sanoojes/SplitKeeb/images/day3/handmade.png

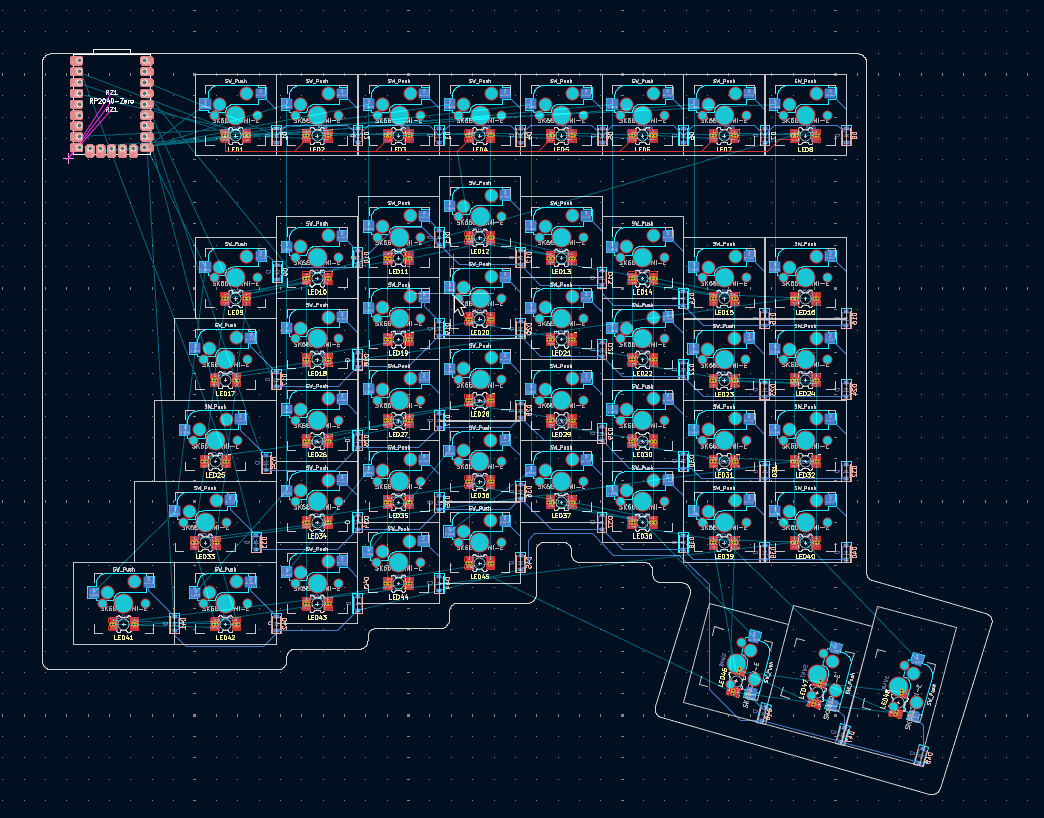
images/day3/handmade.png
