sanoojes/SplitKeeb/images/day4/image.png

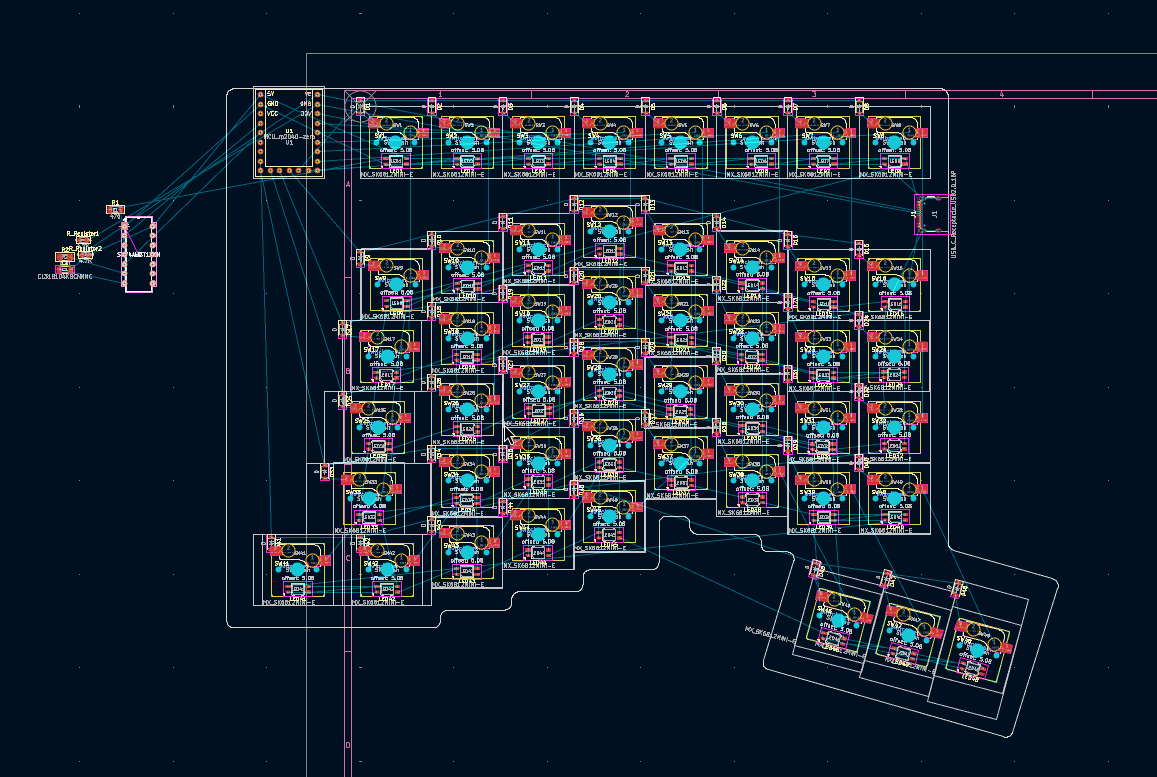
images/day4/image.png
