sanoojes/SplitKeeb/images/day4/new_schema1.png

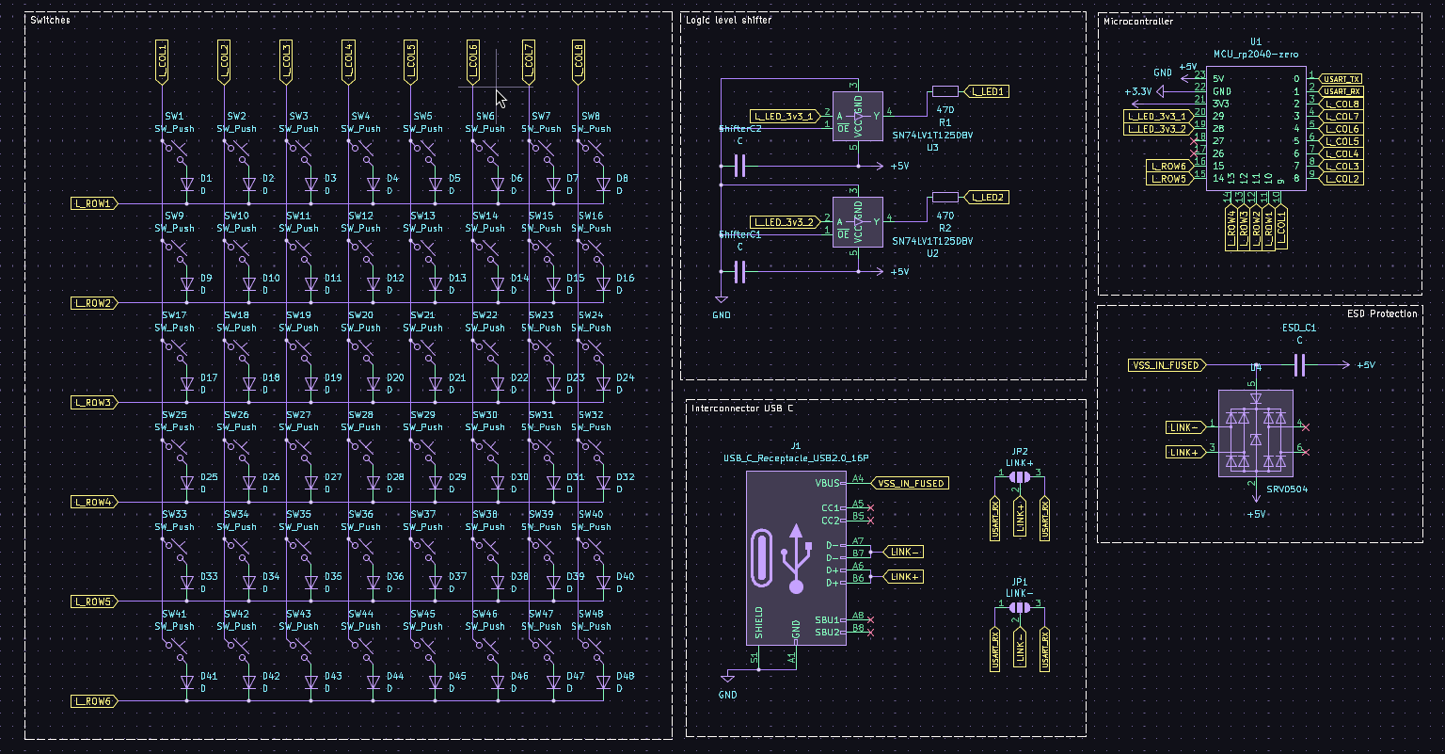
images/day4/new_schema1.png
