sanoojes/SplitKeeb/images/day4/new_schema2.png

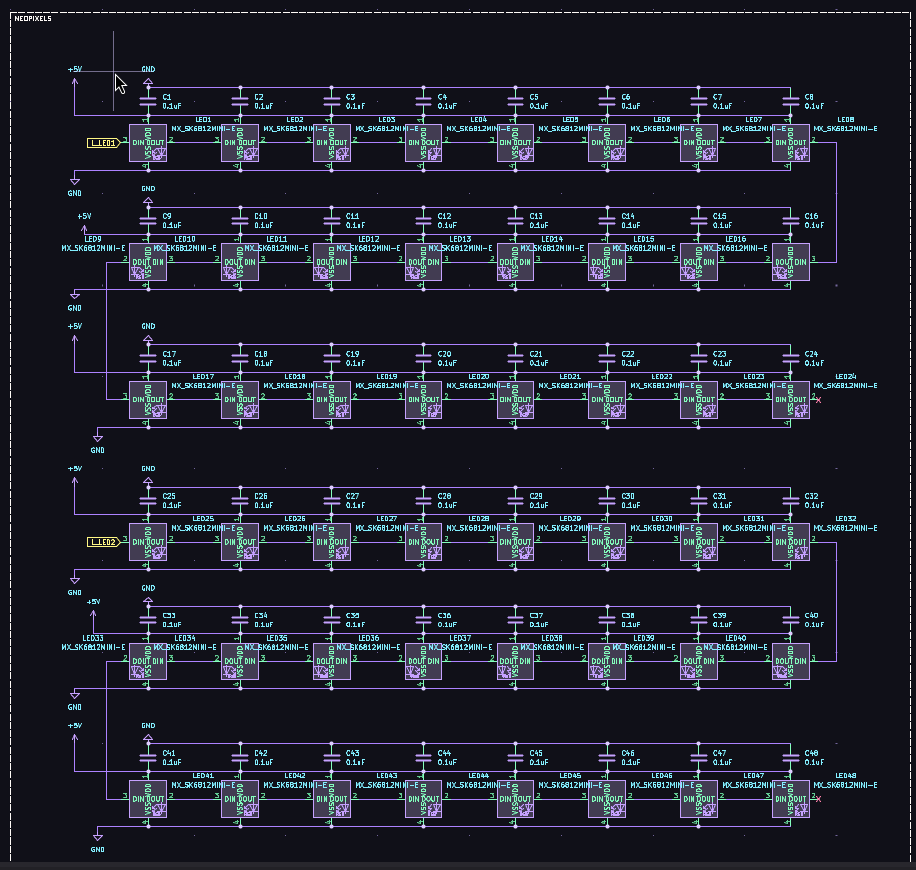
images/day4/new_schema2.png
