sanoojes/SplitKeeb/images/day5/pcb_back.png

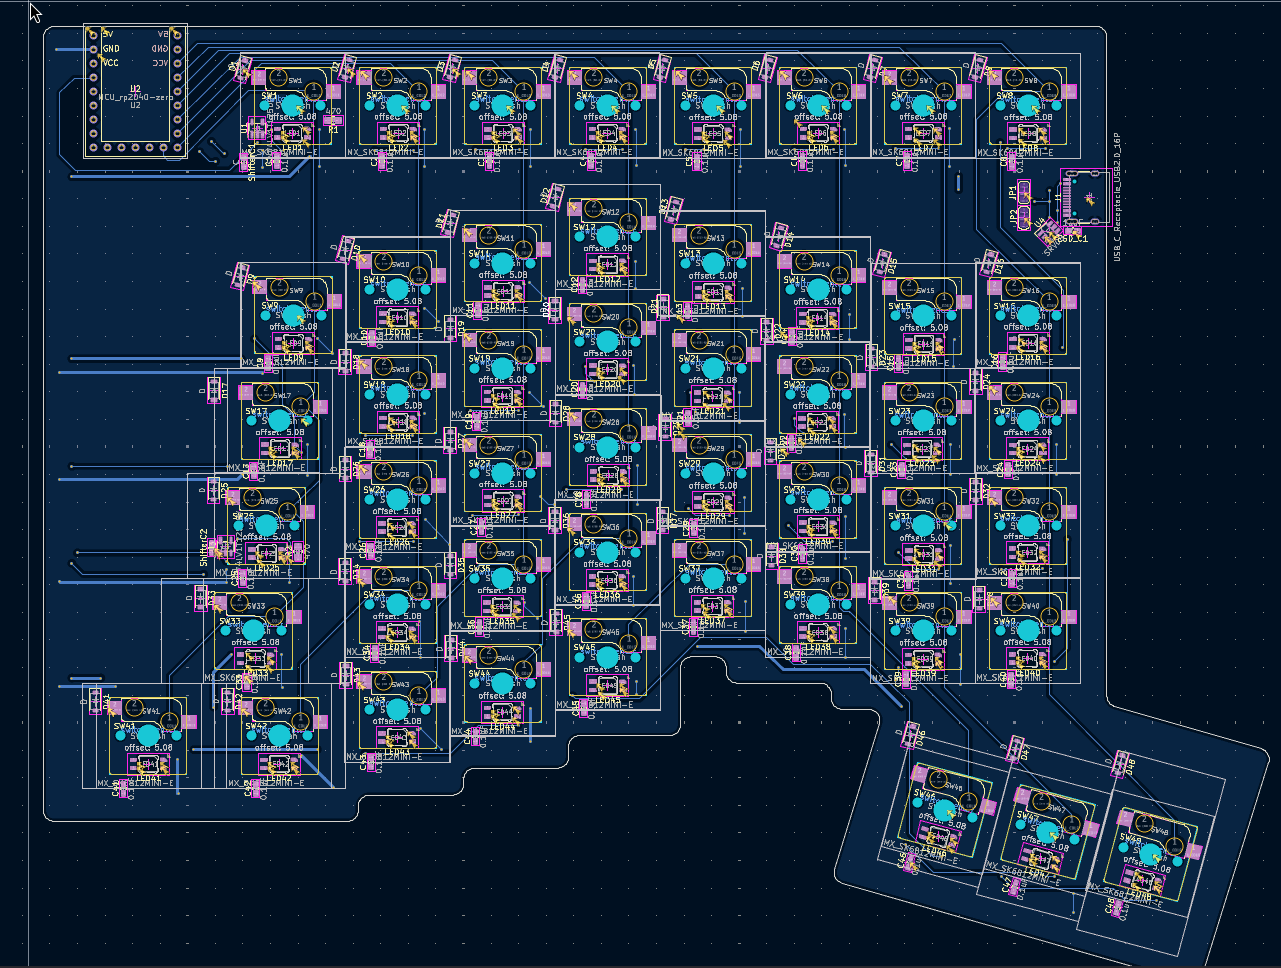
images/day5/pcb_back.png
