sanoojes/SplitKeeb/images/day5/pcb_front.png

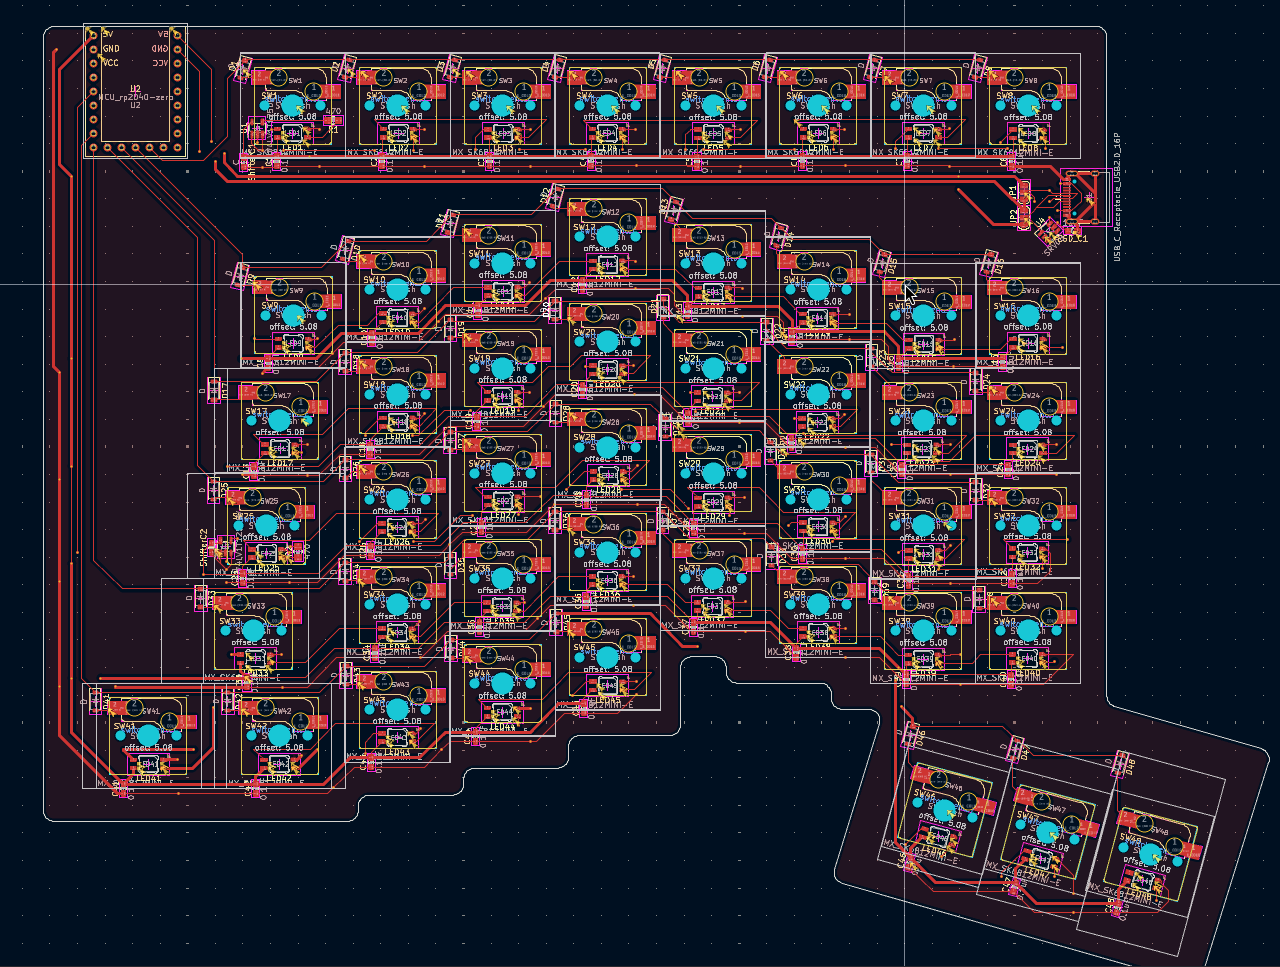
images/day5/pcb_front.png
