sanoojes/SplitKeeb/images/day7/pcb1.png

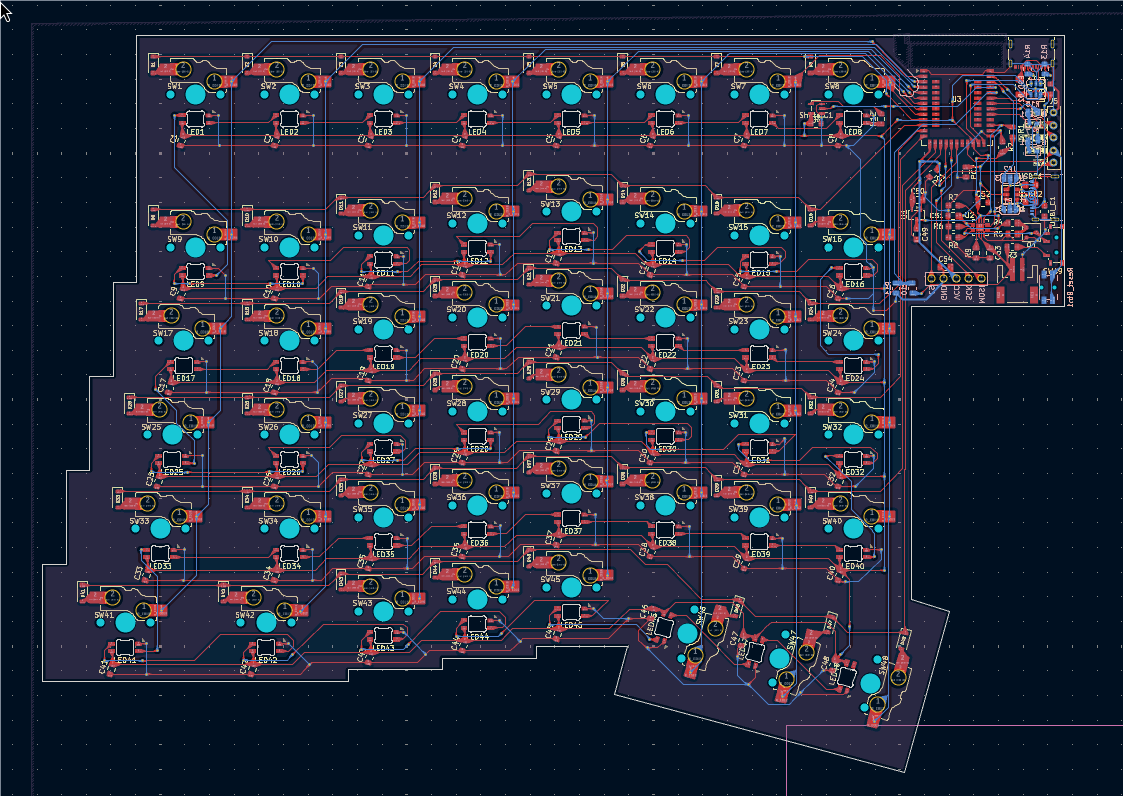
images/day7/pcb1.png
