sanoojes/SplitKeeb/images/day8/3d_back_right.png

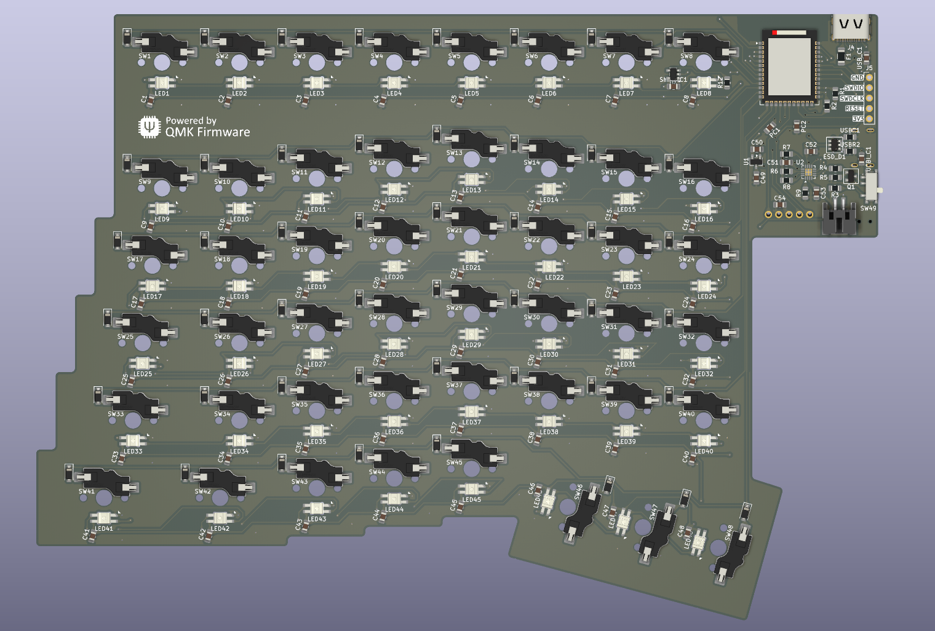
images/day8/3d_back_right.png
