sanoojes/SplitKeeb/images/day8/3d_front_right.png

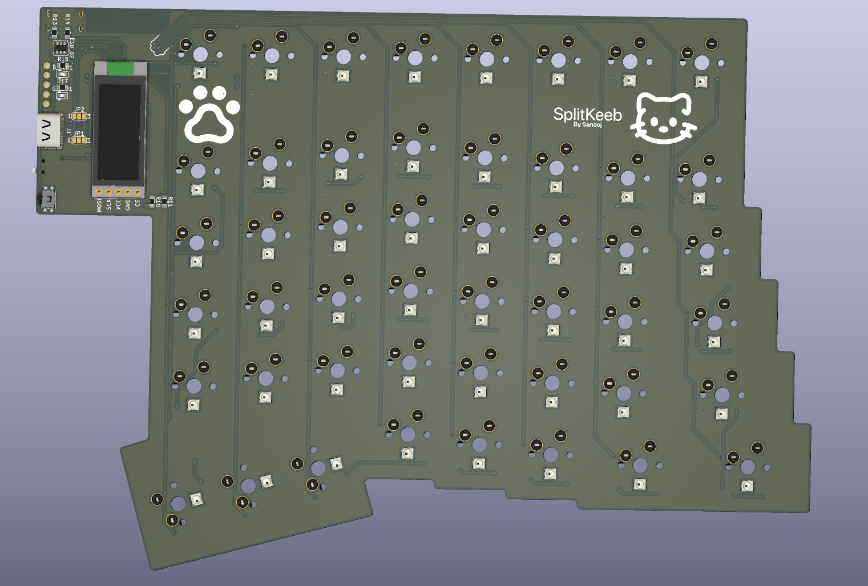
images/day8/3d_front_right.png
