sanoojes/SplitKeeb/images/day8/back_pcb.png

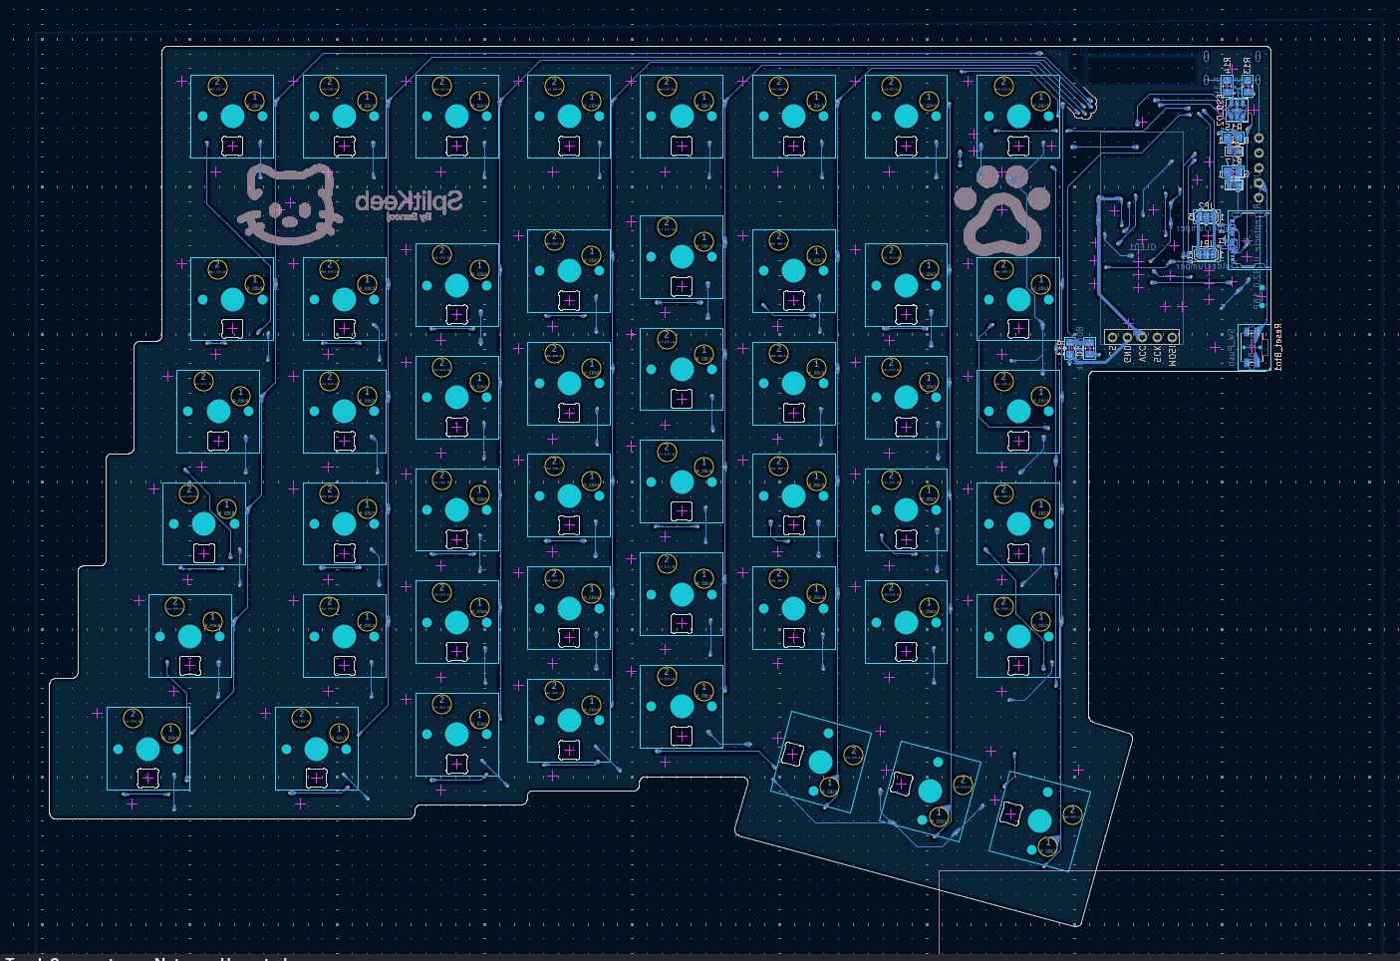
images/day8/back_pcb.png
