sanoojes/SplitKeeb/images/final/schema/right/2.png

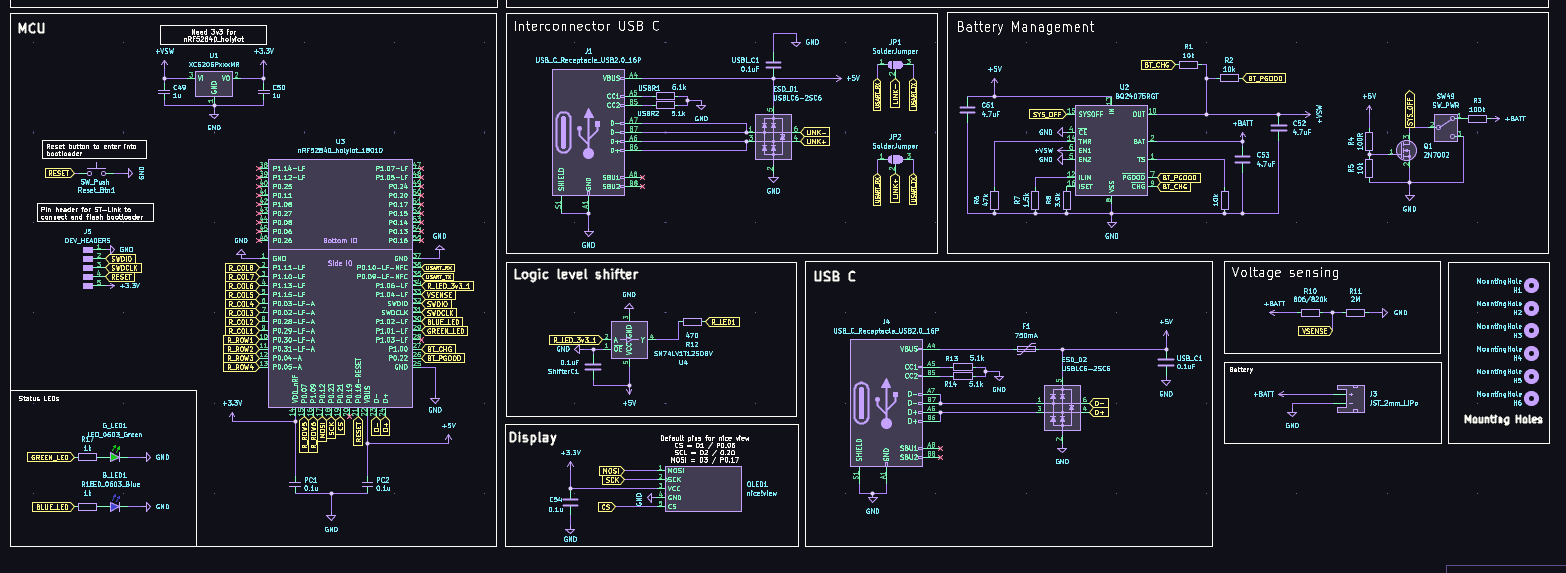
images/final/schema/right/2.png
