sanoojes/SplitKeeb/images/pcb/branding.png

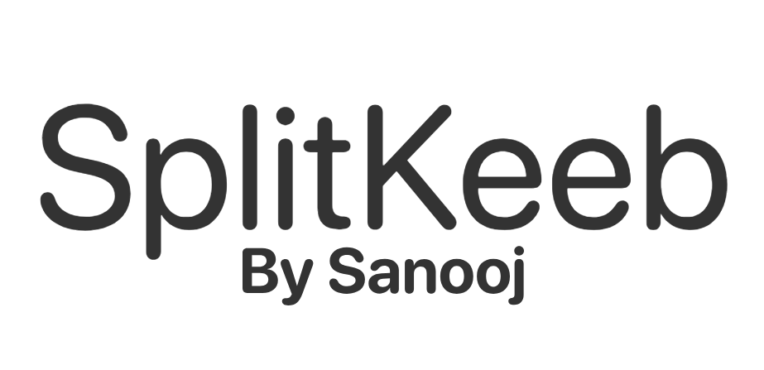
images/pcb/branding.png
