sanoojes/SplitKeeb/images/pcb/cat.png

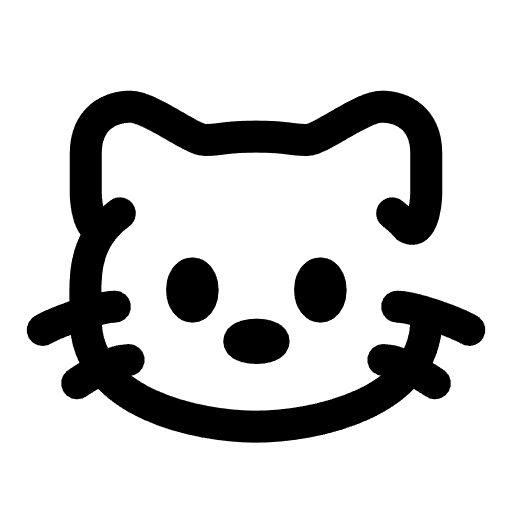
images/pcb/cat.png
