sanoojes/SplitKeeb/images/bom/jlc_cart.png

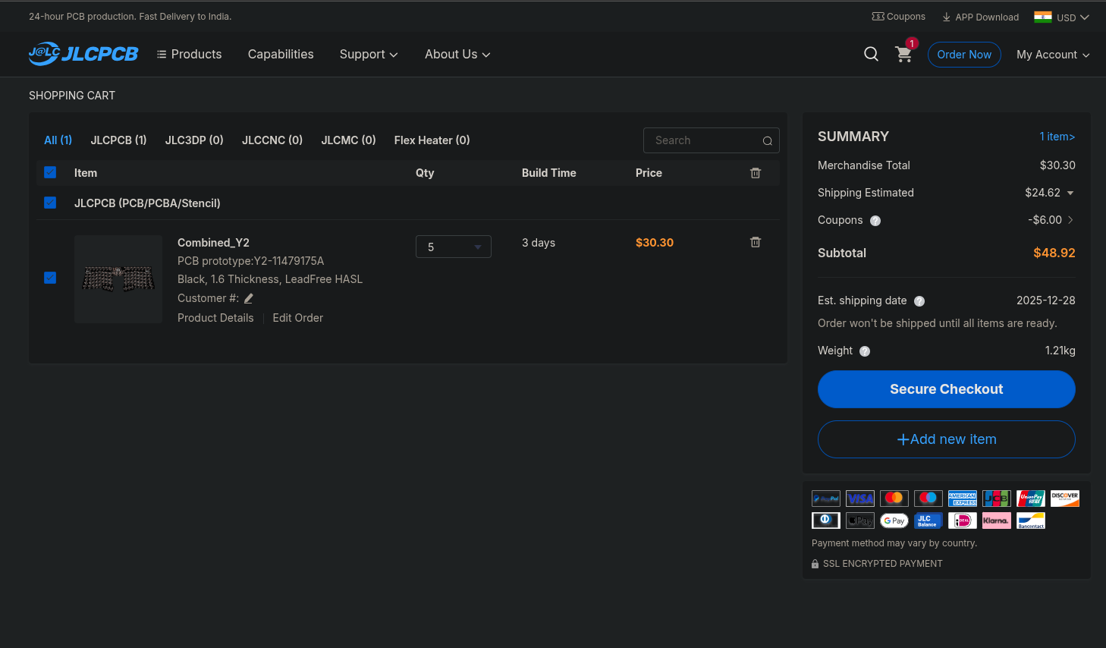
images/bom/jlc_cart.png
