sanoojes/SplitKeeb/images/pcb/paw-print.png

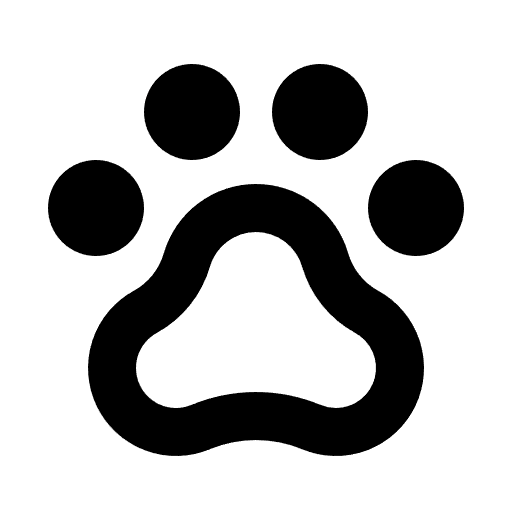
images/pcb/paw-print.png
