sanoojes/SplitKeeb/images/day2/test_1.png

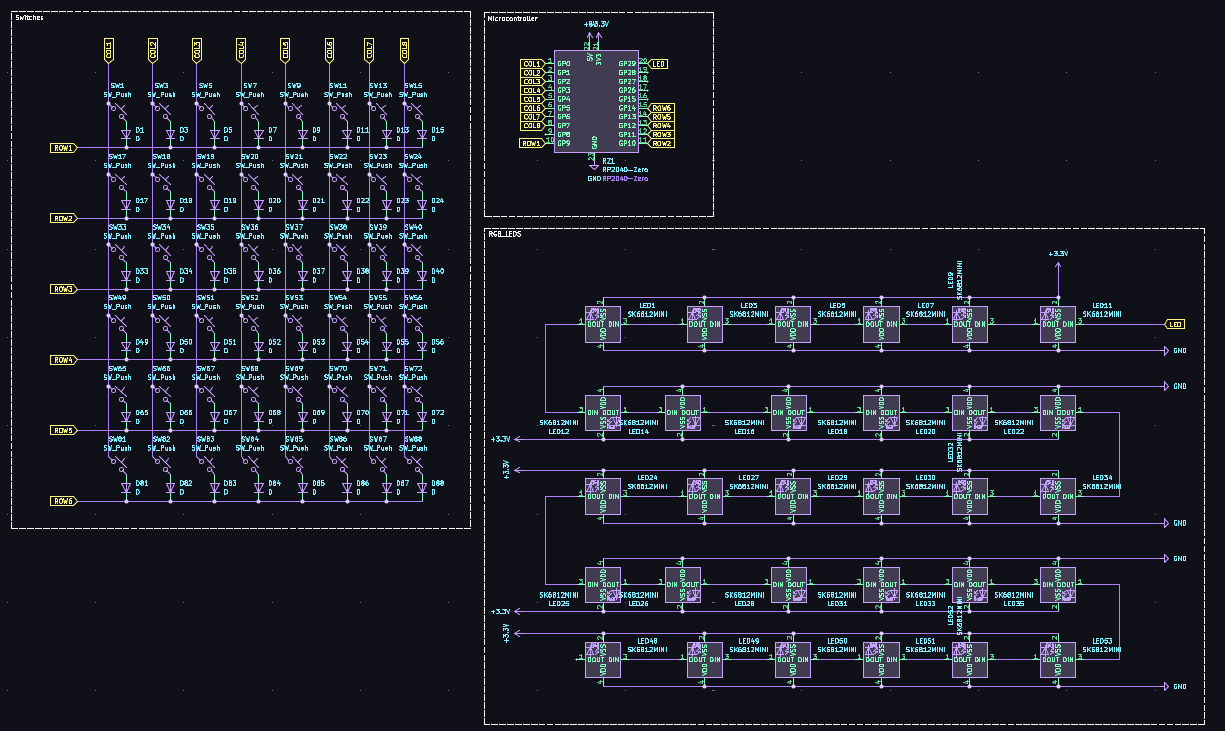
images/day2/test_1.png
