sanoojes/SplitKeeb/pcb/Right/Right.kicad_sch

## KiCad design pcb/Right/Right.kicad_sch (2025-12-22)

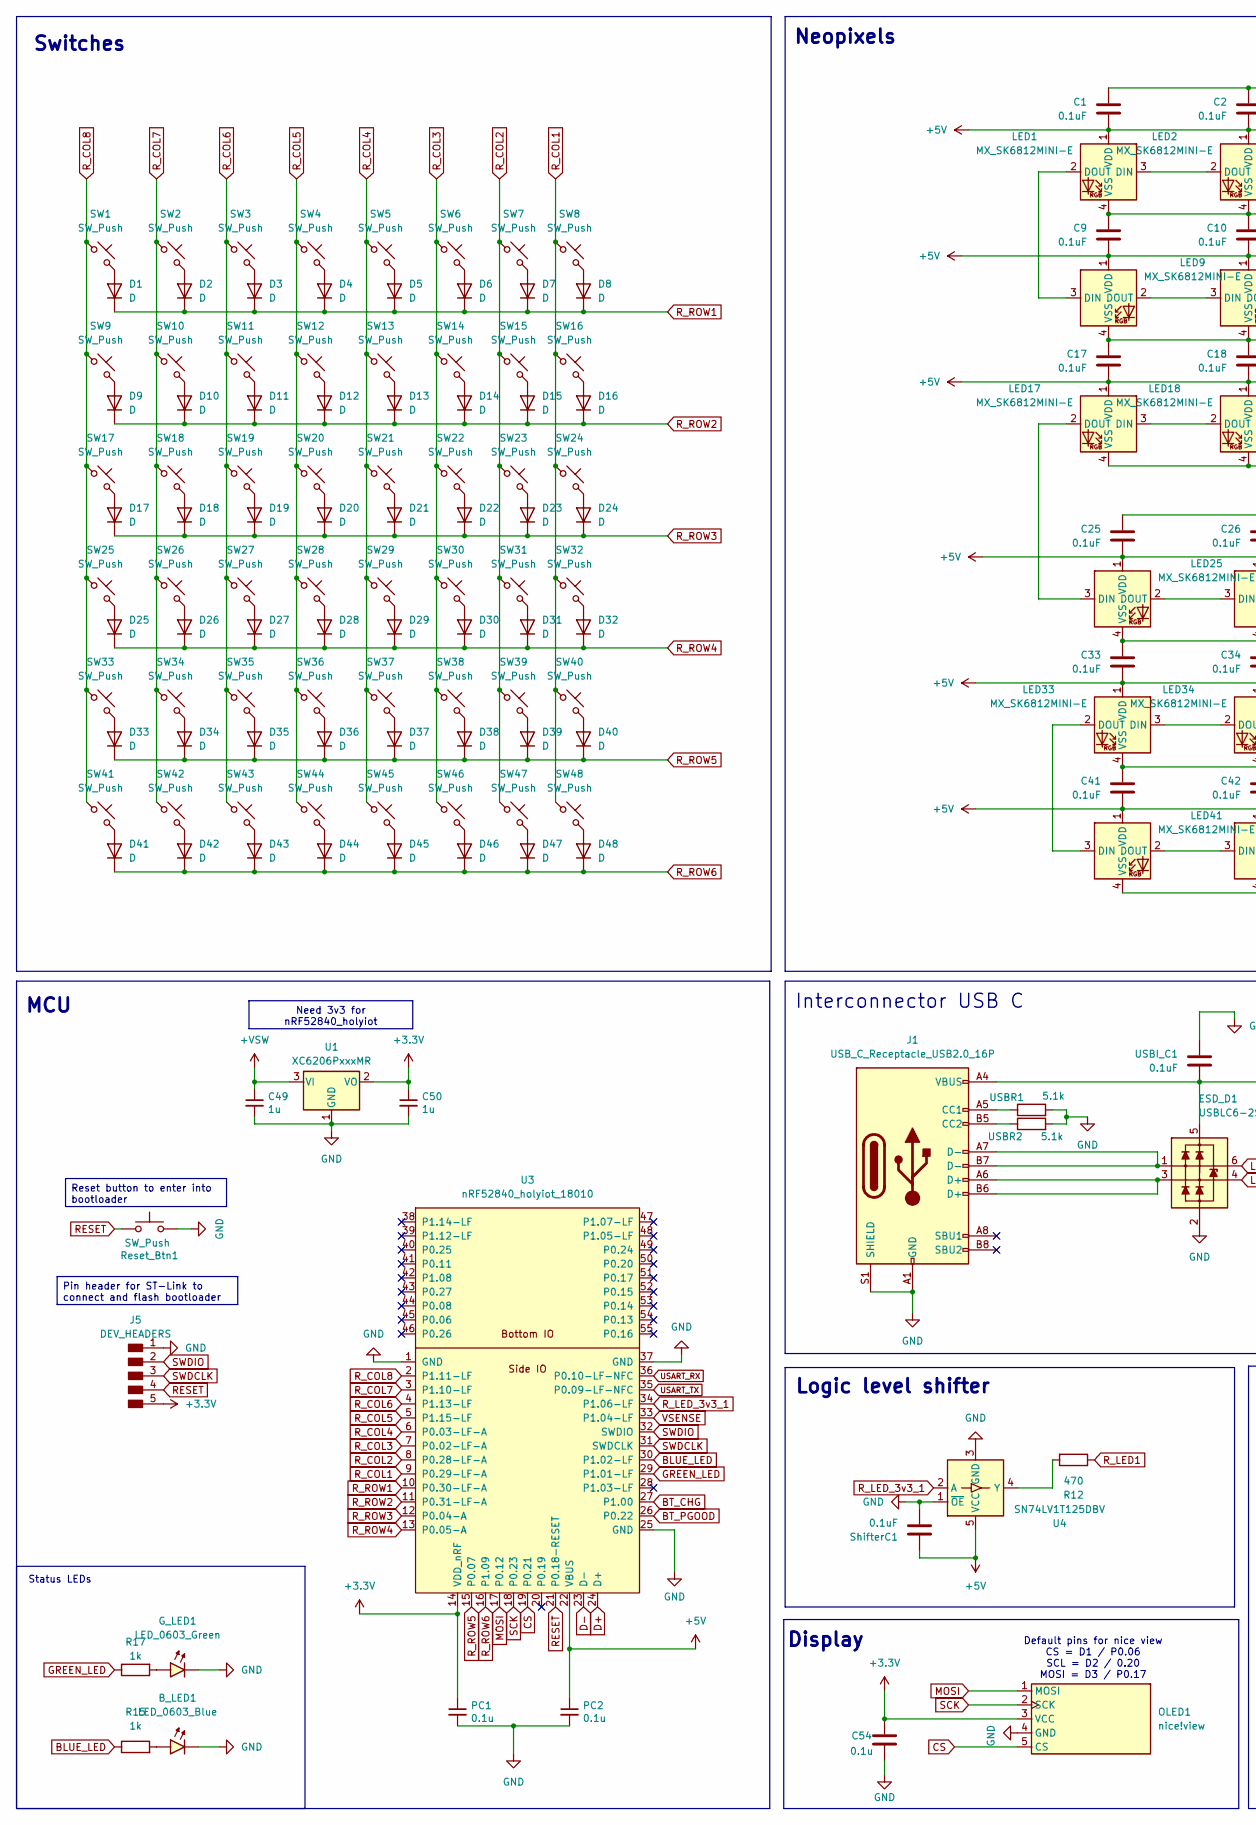
[picture p42: schematic Right.kicad_sch, part in row 1, column 1]

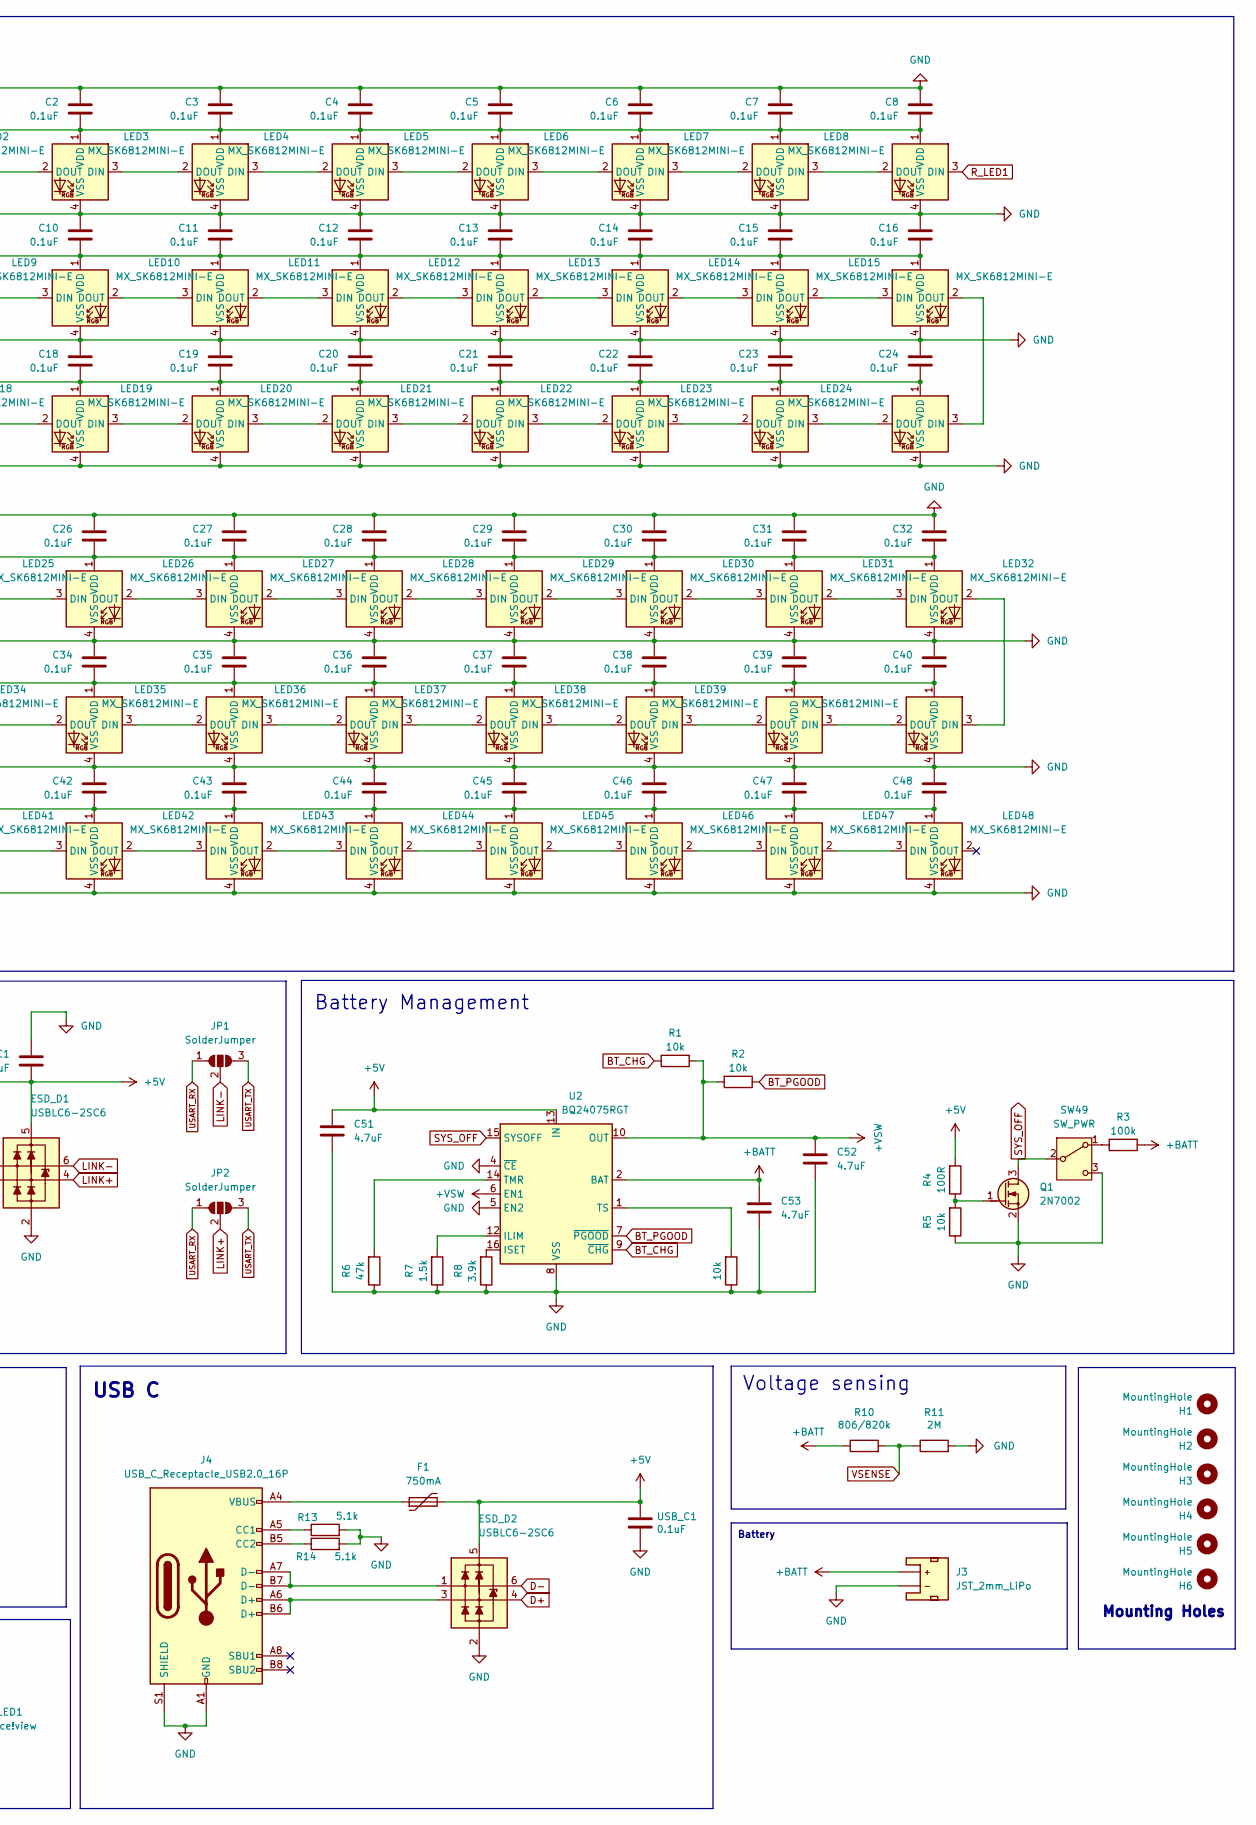
[picture p43: schematic Right.kicad_sch, part in row 1, column 2]

Parts:
B_LED1: LED_0603_Blue; LED_0603_1608Metric
C1, C2, C3, C4, C5, C6, C7, C8, C9, C10, C11, C12, C13, C14, C15, C16, C17, C18, C19, C20, C21, C22, C23, C24, C25, C26, C27, C28, C29, C30, C31, C32, C33, C34, C35, C36, C37, C38, C39, C40, C41, C42, C43, C44, C45, C46, C47, C48: 0.1uF; C_0805_2012Metric_Pad1.18x1.45mm_HandSolder
C49, C50: 1u; C_0805_2012Metric_Pad1.18x1.45mm_HandSolder
C51, C52, C53: 4.7uF; C_0805_2012Metric_Pad1.18x1.45mm_HandSolder
C54: 0.1u; C_0805_2012Metric_Pad1.18x1.45mm_HandSolder
D1, D2, D3, D4, D5, D6, D7, D8, D9, D10, D11, D12, D13, D14, D15, D16, D17, D18, D19, D20, D21, D22, D23, D24, D25, D26, D27, D28, D29, D30, D31, D32, D33, D34, D35, D36, D37, D38, D39, D40, D41, D42, D43, D44, D45, D46, D47, D48: D; D_SOD-123
ESD_D1, ESD_D2: USBLC6-2SC6; SOT-23-6
F1: 750mA; Fuse_1206_3216Metric_Pad1.42x1.75mm_HandSolder; LCSC C135341
G_LED1: LED_0603_Green; LED_0603_1608Metric
H1, H2, H3, H4, H5, H6: MountingHole; MountingHole_3.2mm_M3_Pad_TopBottom
J1, J4: USB_C_Receptacle_USB2.0_16P; USB_C_Receptacle_HRO_TYPE-C-31-M-23
J3: JST_2mm_LiPo; JST_1x02_P2.0mm_Horizontal_SMD
J5: DEV_HEADERS; PinHeader_01x05_P2.54mm_Vertical_THT_D1mm
JP1, JP2: SolderJumper; SolderJumper-3_P1.3mm_Open_RoundedPad1.0x1.5mm_NumberLabels
LED1, LED2, LED3, LED4, LED5, LED6, LED7, LED8, LED9, LED10, LED11, LED12, LED13, LED14, LED15, LED16, LED17, LED18, LED19, LED20, LED21, LED22, LED23, LED24, LED25, LED26, LED27, LED28, LED29, LED30, LED31, LED32, LED33, LED34, LED35, LED36, LED37, LED38, LED39, LED40, LED41, LED42, LED43, LED44, LED45, LED46, LED47, LED48: MX_SK6812MINI-E; LED_MX_6028R-ROT
OLED1: nice!view; nice_view
PC1, PC2: 0.1u; C_0805_2012Metric_Pad1.18x1.45mm_HandSolder
Q1: 2N7002; SOT-23
R1, R2, R5, R9: 10k; R_0805_2012Metric_Pad1.20x1.40mm_HandSolder
R3: 100k; R_0805_2012Metric_Pad1.20x1.40mm_HandSolder
R4: 100R; R_0805_2012Metric_Pad1.20x1.40mm_HandSolder
R6: 47k; R_0805_2012Metric_Pad1.20x1.40mm_HandSolder
R7: 1.5k; R_0805_2012Metric_Pad1.20x1.40mm_HandSolder
R8: 3.9k; R_0805_2012Metric_Pad1.20x1.40mm_HandSolder
R10: 806/820k; R_0805_2012Metric_Pad1.20x1.40mm_HandSolder
R11: 2M; R_0805_2012Metric_Pad1.20x1.40mm_HandSolder
R12: 470; R_0805_2012Metric_Pad1.20x1.40mm_HandSolder
R13, R14: 5.1k; R_0805_2012Metric_Pad1.20x1.40mm_HandSolder
R15, R17: 1k; R_0805_2012Metric_Pad1.20x1.40mm_HandSolder
Reset_Btn1: SW_Push; Panasonic_EVQPUL_EVQPUC; LCSC C79175
SW1, SW2, SW3, SW4, SW5, SW6, SW7, SW8, SW9, SW10, SW11, SW12, SW13, SW14, SW15, SW16, SW18, SW19, SW20, SW21, SW22, SW23, SW24, SW26, SW27, SW28, SW29, SW30, SW31, SW32, SW34, SW35, SW36, SW37, SW38, SW39, SW40, SW43, SW44, SW45: SW_Push; SW_MX_HS_KS-2P02B01-01_1u
SW17, SW46: SW_Push; SW_MX_HS_KS-2P02B01-01_1.25u
SW25, SW41, SW42, SW47: SW_Push; SW_MX_HS_KS-2P02B01-01_1.5u
SW33, SW48: SW_Push; SW_MX_HS_KS-2P02B01-01_1.75u
SW49: SW_PWR; SW_MSK12C02-HB
ShifterC1: 0.1uF; C_0805_2012Metric_Pad1.18x1.45mm_HandSolder
U1: XC6206PxxxMR; SOT-23-3
U2: BQ24075RGT; VQFN-16-1EP_3x3mm_P0.5mm_EP1.6x1.6mm
U3: nRF52840_holyiot_18010
U4: SN74LV1T125DBV; SOT-23-5
USBI_C1: 0.1uF; C_0805_2012Metric_Pad1.18x1.45mm_HandSolder
USBR1, USBR2: 5.1k; R_0805_2012Metric_Pad1.20x1.40mm_HandSolder
USB_C1: 0.1uF; C_0805_2012Metric_Pad1.18x1.45mm_HandSolder; LCSC C307331

Connections:
+3.3V: C50.1, C54.1, J5.5, OLED1.3 (VCC), PC1.1, U1.2 (VO), U3.14 (VDD_nRF)
+5V: C1.2, C2.2, C3.2, C4.2, C5.2, C6.2, C7.2, C8.2, C9.2, C10.2, C11.2, C12.2, C13.2, C14.2, C15.2, C16.2, C17.2, C18.2, C19.2, C20.2, C21.2, C22.2, C23.2, C24.2, C25.2, C26.2, C27.2, C28.2, C29.2, C30.2, C31.2, C32.2, C33.2, C34.2, C35.2, C36.2, C37.2, C38.2, C39.2, C40.2, C41.2, C42.2, C43.2, C44.2, C45.2, C46.2, C47.2, C48.2, C51.1, ESD_D1.5 (VP), ESD_D2.5 (VP), F1.2, J1.A4 (VBUS), J1.A9 (VBUS), J1.B4 (VBUS), J1.B9 (VBUS), LED1.1 (VDD), LED2.1 (VDD), LED3.1 (VDD), LED4.1 (VDD), LED5.1 (VDD), LED6.1 (VDD), LED7.1 (VDD), LED8.1 (VDD), LED9.1 (VDD), LED10.1 (VDD), LED11.1 (VDD), LED12.1 (VDD), LED13.1 (VDD), LED14.1 (VDD), LED15.1 (VDD), LED16.1 (VDD), LED17.1 (VDD), LED18.1 (VDD), LED19.1 (VDD), LED20.1 (VDD), LED21.1 (VDD), LED22.1 (VDD), LED23.1 (VDD), LED24.1 (VDD), LED25.1 (VDD), LED26.1 (VDD), LED27.1 (VDD), LED28.1 (VDD), LED29.1 (VDD), LED30.1 (VDD), LED31.1 (VDD), LED32.1 (VDD), LED33.1 (VDD), LED34.1 (VDD), LED35.1 (VDD), LED36.1 (VDD), LED37.1 (VDD), LED38.1 (VDD), LED39.1 (VDD), LED40.1 (VDD), LED41.1 (VDD), LED42.1 (VDD), LED43.1 (VDD), LED44.1 (VDD), LED45.1 (VDD), LED46.1 (VDD), LED47.1 (VDD), LED48.1 (VDD), PC2.1, R4.2, ShifterC1.1, U2.13 (IN), U3.22 (VBUS), U4.5 (VCC), USBI_C1.1, USB_C1.1
+BATT: C53.1, J3.2 (+), R3.2, R10.1, U2.2 (BAT), U2.3 (BAT)
+VSW: C49.1, C52.1, R1.2, R2.2, U1.3 (VI), U2.6 (EN1), U2.10 (OUT), U2.11 (OUT)
BLUE_LED: R15.1, U3.30 (P1.02-LF)
BT_CHG: R1.1, U2.9 (~CHG), U3.27 (P1.00)
BT_PGOOD: R2.1, U2.7 (~PGOOD), U3.26 (P0.22)
CS: OLED1.5 (CS), U3.19 (P0.21)
D+: ESD_D2.4 (L2), U3.24 (D+)
D-: ESD_D2.6 (L1), U3.23 (D-)
GND: B_LED1.1 (K), C1.1, C2.1, C3.1, C4.1, C5.1, C6.1, C7.1, C8.1, C9.1, C10.1, C11.1, C12.1, C13.1, C14.1, C15.1, C16.1, C17.1, C18.1, C19.1, C20.1, C21.1, C22.1, C23.1, C24.1, C25.1, C26.1, C27.1, C28.1, C29.1, C30.1, C31.1, C32.1, C33.1, C34.1, C35.1, C36.1, C37.1, C38.1, C39.1, C40.1, C41.1, C42.1, C43.1, C44.1, C45.1, C46.1, C47.1, C48.1, C49.2, C50.2, C51.2, C52.2, C53.2, C54.2, ESD_D1.2 (VN), ESD_D2.2 (VN), G_LED1.1 (K), J1.A1 (GND), J1.A12 (GND), J1.B1 (GND), J1.B12 (GND), J1.S1 (SHIELD), J3.1 (-), J4.A1 (GND), J4.A12 (GND), J4.B1 (GND), J4.B12 (GND), J4.S1 (SHIELD), J5.1, LED1.4 (VSS), LED2.4 (VSS), LED3.4 (VSS), LED4.4 (VSS), LED5.4 (VSS), LED6.4 (VSS), LED7.4 (VSS), LED8.4 (VSS), LED9.4 (VSS), LED10.4 (VSS), LED11.4 (VSS), LED12.4 (VSS), LED13.4 (VSS), LED14.4 (VSS), LED15.4 (VSS), LED16.4 (VSS), LED17.4 (VSS), LED18.4 (VSS), LED19.4 (VSS), LED20.4 (VSS), LED21.4 (VSS), LED22.4 (VSS), LED23.4 (VSS), LED24.4 (VSS), LED25.4 (VSS), LED26.4 (VSS), LED27.4 (VSS), LED28.4 (VSS), LED29.4 (VSS), LED30.4 (VSS), LED31.4 (VSS), LED32.4 (VSS), LED33.4 (VSS), LED34.4 (VSS), LED35.4 (VSS), LED36.4 (VSS), LED37.4 (VSS), LED38.4 (VSS), LED39.4 (VSS), LED40.4 (VSS), LED41.4 (VSS), LED42.4 (VSS), LED43.4 (VSS), LED44.4 (VSS), LED45.4 (VSS), LED46.4 (VSS), LED47.4 (VSS), LED48.4 (VSS), OLED1.4 (GND), PC1.2, PC2.2, Q1.2 (S), R5.1, R6.1, R7.1, R8.1, R9.1, R11.2, R13.2, R14.2, Reset_Btn1.2, SW49.3 (C), ShifterC1.2, U1.1 (GND), U2.4 (~CE), U2.5 (EN2), U2.8 (VSS), U2.17 (VSS), U3.1 (GND), U3.25 (GND), U3.37 (GND), U4.1 (~OE), U4.3 (GND), USBI_C1.2, USBR1.2, USBR2.2, USB_C1.2
GREEN_LED: R17.1, U3.29 (P1.01-LF)
LINK+: ESD_D1.4 (L2), JP2.2 (C)
LINK-: ESD_D1.6 (L1), JP1.2 (C)
MOSI: OLED1.1 (MOSI), U3.17 (P0.12)
unnamed: B_LED1.2 (A), R15.2
unnamed: D1.2 (A), SW1.2
unnamed: D2.2 (A), SW2.2
unnamed: D3.2 (A), SW3.2
unnamed: D4.2 (A), SW4.2
unnamed: D5.2 (A), SW5.2
unnamed: D6.2 (A), SW6.2
unnamed: D7.2 (A), SW7.2
unnamed: D8.2 (A), SW8.2
unnamed: D9.2 (A), SW9.2
unnamed: D10.2 (A), SW10.2
unnamed: D11.2 (A), SW11.2
unnamed: D12.2 (A), SW12.2
unnamed: D13.2 (A), SW13.2
unnamed: D14.2 (A), SW14.2
unnamed: D15.2 (A), SW15.2
unnamed: D16.2 (A), SW16.2
unnamed: D17.2 (A), SW17.2
unnamed: D18.2 (A), SW18.2
unnamed: D19.2 (A), SW19.2
unnamed: D20.2 (A), SW20.2
unnamed: D21.2 (A), SW21.2
unnamed: D22.2 (A), SW22.2
unnamed: D23.2 (A), SW23.2
unnamed: D24.2 (A), SW24.2
unnamed: D25.2 (A), SW25.2
unnamed: D26.2 (A), SW26.2
unnamed: D27.2 (A), SW27.2
unnamed: D28.2 (A), SW28.2
unnamed: D29.2 (A), SW29.2
unnamed: D30.2 (A), SW30.2
unnamed: D31.2 (A), SW31.2
unnamed: D32.2 (A), SW32.2
unnamed: D33.2 (A), SW33.2
unnamed: D34.2 (A), SW34.2
unnamed: D35.2 (A), SW35.2
unnamed: D36.2 (A), SW36.2
unnamed: D37.2 (A), SW37.2
unnamed: D38.2 (A), SW38.2
unnamed: D39.2 (A), SW39.2
unnamed: D40.2 (A), SW40.2
unnamed: D41.2 (A), SW41.2
unnamed: D42.2 (A), SW42.2
unnamed: D43.2 (A), SW43.2
unnamed: D44.2 (A), SW44.2
unnamed: D45.2 (A), SW45.2
unnamed: D46.2 (A), SW46.2
unnamed: D47.2 (A), SW47.2
unnamed: D48.2 (A), SW48.2
unnamed: ESD_D1.1 (L1), J1.A7 (D-), J1.B7 (D-)
unnamed: ESD_D1.3 (L2), J1.A6 (D+), J1.B6 (D+)
unnamed: ESD_D2.1 (L1), J4.A7 (D-), J4.B7 (D-)
unnamed: ESD_D2.3 (L2), J4.A6 (D+), J4.B6 (D+)
unnamed: F1.1, J4.A4 (VBUS), J4.A9 (VBUS), J4.B4 (VBUS), J4.B9 (VBUS)
unnamed: G_LED1.2 (A), R17.2
unnamed: J1.A5 (CC1), USBR1.1
unnamed: J1.B5 (CC2), USBR2.1
unnamed: J4.A5 (CC1), R13.1
unnamed: J4.B5 (CC2), R14.1
unnamed: LED1.2 (DOUT), LED9.3 (DIN)
unnamed: LED1.3 (DIN), LED2.2 (DOUT)
unnamed: LED2.3 (DIN), LED3.2 (DOUT)
unnamed: LED3.3 (DIN), LED4.2 (DOUT)
unnamed: LED4.3 (DIN), LED5.2 (DOUT)
unnamed: LED5.3 (DIN), LED6.2 (DOUT)
unnamed: LED6.3 (DIN), LED7.2 (DOUT)
unnamed: LED7.3 (DIN), LED8.2 (DOUT)
unnamed: LED10.2 (DOUT), LED11.3 (DIN)
unnamed: LED9.2 (DOUT), LED10.3 (DIN)
unnamed: LED11.2 (DOUT), LED12.3 (DIN)
unnamed: LED12.2 (DOUT), LED13.3 (DIN)
unnamed: LED13.2 (DOUT), LED14.3 (DIN)
unnamed: LED14.2 (DOUT), LED15.3 (DIN)
unnamed: LED15.2 (DOUT), LED16.3 (DIN)
unnamed: LED16.2 (DOUT), LED24.3 (DIN)
unnamed: LED17.2 (DOUT), LED25.3 (DIN)
unnamed: LED17.3 (DIN), LED18.2 (DOUT)
unnamed: LED18.3 (DIN), LED19.2 (DOUT)
unnamed: LED19.3 (DIN), LED20.2 (DOUT)
unnamed: LED20.3 (DIN), LED21.2 (DOUT)
unnamed: LED21.3 (DIN), LED22.2 (DOUT)
unnamed: LED22.3 (DIN), LED23.2 (DOUT)
unnamed: LED23.3 (DIN), LED24.2 (DOUT)
unnamed: LED25.2 (DOUT), LED26.3 (DIN)
unnamed: LED26.2 (DOUT), LED27.3 (DIN)
unnamed: LED27.2 (DOUT), LED28.3 (DIN)
unnamed: LED28.2 (DOUT), LED29.3 (DIN)
unnamed: LED29.2 (DOUT), LED30.3 (DIN)
unnamed: LED30.2 (DOUT), LED31.3 (DIN)
unnamed: LED31.2 (DOUT), LED32.3 (DIN)
unnamed: LED32.2 (DOUT), LED40.3 (DIN)
unnamed: LED33.2 (DOUT), LED41.3 (DIN)
unnamed: LED33.3 (DIN), LED34.2 (DOUT)
unnamed: LED34.3 (DIN), LED35.2 (DOUT)
unnamed: LED35.3 (DIN), LED36.2 (DOUT)
unnamed: LED36.3 (DIN), LED37.2 (DOUT)
unnamed: LED37.3 (DIN), LED38.2 (DOUT)
unnamed: LED38.3 (DIN), LED39.2 (DOUT)
unnamed: LED39.3 (DIN), LED40.2 (DOUT)
unnamed: LED41.2 (DOUT), LED42.3 (DIN)
unnamed: LED42.2 (DOUT), LED43.3 (DIN)
unnamed: LED43.2 (DOUT), LED44.3 (DIN)
unnamed: LED44.2 (DOUT), LED45.3 (DIN)
unnamed: LED45.2 (DOUT), LED46.3 (DIN)
unnamed: LED46.2 (DOUT), LED47.3 (DIN)
unnamed: LED47.2 (DOUT), LED48.3 (DIN)
unnamed: Q1.1 (G), R4.1, R5.2
unnamed: R3.1, SW49.1 (A)
unnamed: R6.2, U2.14 (TMR)
unnamed: R7.2, U2.12 (ILIM)
unnamed: R8.2, U2.16 (ISET)
unnamed: R9.2, U2.1 (TS)
unnamed: R12.2, U4.4 (Y)
RESET: J5.4, Reset_Btn1.1, U3.21 (P0.18-RESET)
R_COL1: SW8.1, SW16.1, SW24.1, SW32.1, SW40.1, SW48.1, U3.9 (P0.29-LF-A)
R_COL2: SW7.1, SW15.1, SW23.1, SW31.1, SW39.1, SW47.1, U3.8 (P0.28-LF-A)
R_COL3: SW6.1, SW14.1, SW22.1, SW30.1, SW38.1, SW46.1, U3.7 (P0.02-LF-A)
R_COL4: SW5.1, SW13.1, SW21.1, SW29.1, SW37.1, SW45.1, U3.6 (P0.03-LF-A)
R_COL5: SW4.1, SW12.1, SW20.1, SW28.1, SW36.1, SW44.1, U3.5 (P1.15-LF)
R_COL6: SW3.1, SW11.1, SW19.1, SW27.1, SW35.1, SW43.1, U3.4 (P1.13-LF)
R_COL7: SW2.1, SW10.1, SW18.1, SW26.1, SW34.1, SW42.1, U3.3 (P1.10-LF)
R_COL8: SW1.1, SW9.1, SW17.1, SW25.1, SW33.1, SW41.1, U3.2 (P1.11-LF)
R_LED1: LED8.3 (DIN), R12.1
R_LED_3v3_1: U3.34 (P1.06-LF), U4.2 (A)
R_ROW1: D1.1 (K), D2.1 (K), D3.1 (K), D4.1 (K), D5.1 (K), D6.1 (K), D7.1 (K), D8.1 (K), U3.10 (P0.30-LF-A)
R_ROW2: D9.1 (K), D10.1 (K), D11.1 (K), D12.1 (K), D13.1 (K), D14.1 (K), D15.1 (K), D16.1 (K), U3.11 (P0.31-LF-A)
R_ROW3: D17.1 (K), D18.1 (K), D19.1 (K), D20.1 (K), D21.1 (K), D22.1 (K), D23.1 (K), D24.1 (K), U3.12 (P0.04-A)
R_ROW4: D25.1 (K), D26.1 (K), D27.1 (K), D28.1 (K), D29.1 (K), D30.1 (K), D31.1 (K), D32.1 (K), U3.13 (P0.05-A)
R_ROW5: D33.1 (K), D34.1 (K), D35.1 (K), D36.1 (K), D37.1 (K), D38.1 (K), D39.1 (K), D40.1 (K), U3.15 (P0.07)
R_ROW6: D41.1 (K), D42.1 (K), D43.1 (K), D44.1 (K), D45.1 (K), D46.1 (K), D47.1 (K), D48.1 (K), U3.16 (P1.09)
SCK: OLED1.2 (SCK), U3.18 (P0.23)
SWDCLK: J5.3, U3.31 (SWDCLK)
SWDIO: J5.2, U3.32 (SWDIO)
SYS_OFF: Q1.3 (D), SW49.2 (B), U2.15 (SYSOFF)
USART_RX: JP1.1 (A), JP2.1 (A), U3.36 (P0.10-LF-NFC)
USART_TX: JP1.3 (B), JP2.3 (B), U3.35 (P0.09-LF-NFC)
VSENSE: R10.2, R11.1, U3.33 (P1.04-LF)

Notes on the sheet:
Voltage sensing
Display
Default pins for nice view CS = D1 / P0.06 SCL = D2 / 0.20 MOSI = D3 / P0.17
Status LEDs
Mounting Holes
Logic level shifter
Neopixels
Interconnector USB C
MCU
Switches
Battery Management
Battery
USB C
Need 3v3 for nRF52840_holyiot
Pin header for ST-Link to connect and flash bootloader
Reset button to enter into bootloader
